Gabor944/phonefarm/pictures/pi_connection_greenlight.jpg

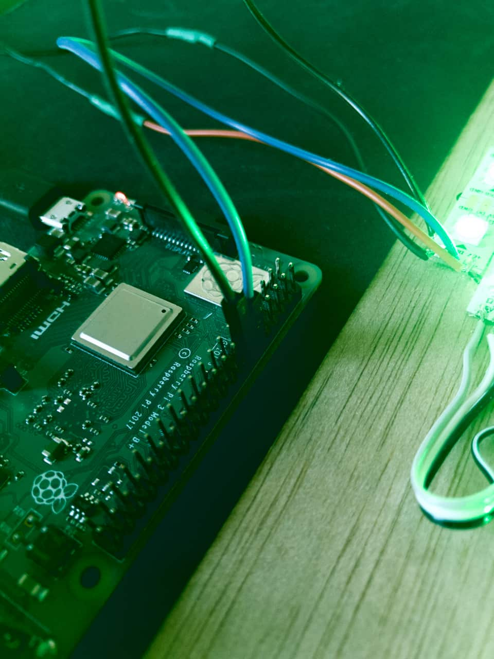
pictures/pi_connection_greenlight.jpg
