Gabor944/phonefarm/pictures/screws.jpg

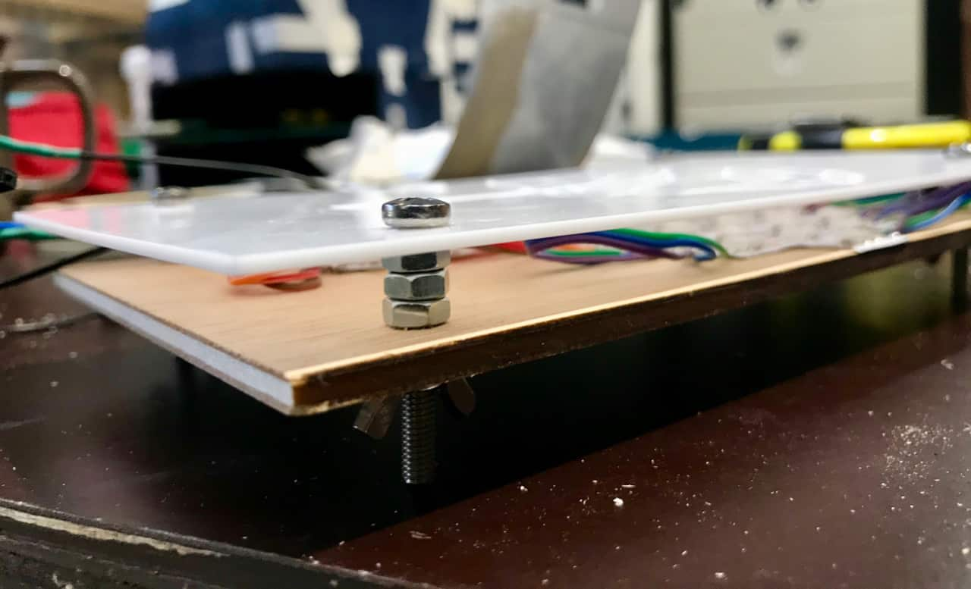
pictures/screws.jpg
